Scruchet/custom_guitar_pedals/simulation/circuits.asc

C6: polcap; 47µ
C8: polcap; 100µ
C9: polcap; 10µ
C10: cap; 33n
C11: polcap; 10µ
C12: polcap; 47µ
C13: polcap; 22µ
D4: diode
D5: diode
Q2: npn; 2N3904
Q3: npn; 2N3904
Q4: npn; 2N3904
R11: res; 3.3k
R12: res; 22k
R13: res; 5.6k
R14: res; 1k
R15: res; 500
R16: res; 3.3k
R17: res; 0
R18: res; 33k
R19: res; 4.7k
R20: res; 330
R21: res; 100k
R22: res; 500
R23: res; 0
R24: res; 500k
R25: res; 500
R27: res; 50k
R28: res; 50k
R29: res; 1k
R30: res; 1000k
V1: voltage; 9
V2: voltage; SINE(0 1 500)
Named nets: 0, VCC, in
.tran 0 10m 1m
